StonedEdge/Retro-Lite-CM4-Dock/consolevectors/gb/DMG -High Tech Transparent (1995) (US).png

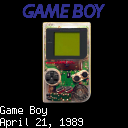
consolevectors/gb/DMG -High Tech Transparent (1995) (US).png
