StonedEdge/Retro-Lite-CM4-Dock/consolevectors/dreamcast/Dreamcast - Black.png

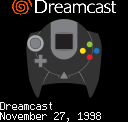
consolevectors/dreamcast/Dreamcast - Black.png
