StonedEdge/Retro-Lite-CM4-Dock/consolevectors/dreamcast/Dreamcast - Grey.png

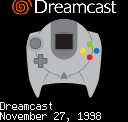
consolevectors/dreamcast/Dreamcast - Grey.png
