StonedEdge/Retro-Lite-CM4-Dock/consolevectors/dreamcast/Dreamcast - Red.png

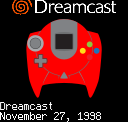
consolevectors/dreamcast/Dreamcast - Red.png
