StonedEdge/Retro-Lite-CM4-Dock/consolevectors/famicom/Famicom.png

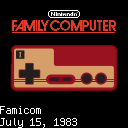
consolevectors/famicom/Famicom.png
