StonedEdge/Retro-Lite-CM4-Dock/consolevectors/gamegear/Game Gear.png

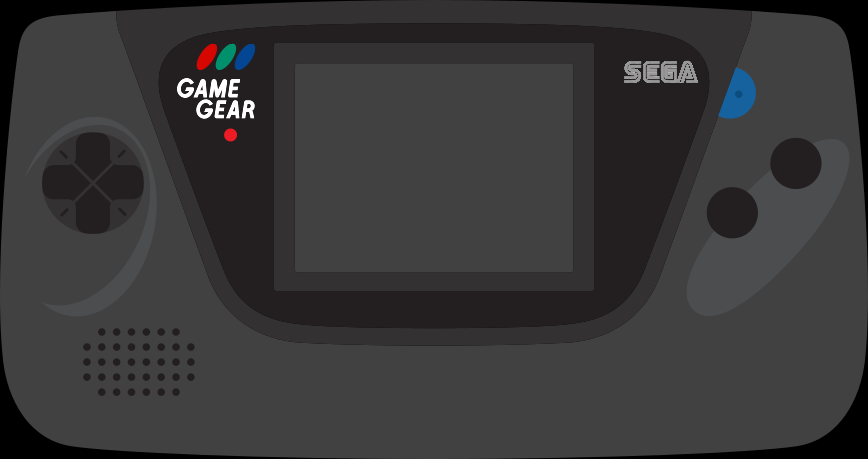
consolevectors/gamegear/Game Gear.png
