StonedEdge/Retro-Lite-CM4-Dock/consolevectors/gb/DMG - Cool Blue (1995) (EU).png

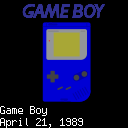
consolevectors/gb/DMG - Cool Blue (1995) (EU).png
