StonedEdge/Retro-Lite-CM4-Dock/consolevectors/gb/DMG - Deep Black (1995).png

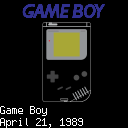
consolevectors/gb/DMG - Deep Black (1995).png
