StonedEdge/Retro-Lite-CM4-Dock/consolevectors/gb/DMG - Off White.png

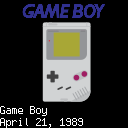
consolevectors/gb/DMG - Off White.png
