StonedEdge/Retro-Lite-CM4-Dock/consolevectors/gb/DMG - Radiant Red (1995).png

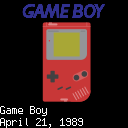
consolevectors/gb/DMG - Radiant Red (1995).png
