StonedEdge/Retro-Lite-CM4-Dock/consolevectors/gba/Gameboy Micro - Black.png

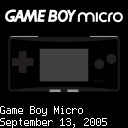
consolevectors/gba/Gameboy Micro - Black.png
