StonedEdge/Retro-Lite-CM4-Dock/consolevectors/gba/Gameboy Micro - Blue.png

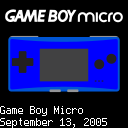
consolevectors/gba/Gameboy Micro - Blue.png
