StonedEdge/Retro-Lite-CM4-Dock/consolevectors/gba/Gameboy Micro - Famicom - red w gold faceplate (Japan, 2005).png

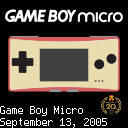
consolevectors/gba/Gameboy Micro - Famicom - red w gold faceplate (Japan, 2005).png
