StonedEdge/Retro-Lite-CM4-Dock/consolevectors/gba/Gameboy Micro - Mother 3 - red w red, worn faceplate (Japan, 2006).png

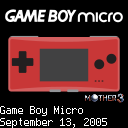
consolevectors/gba/Gameboy Micro - Mother 3 - red w red, worn faceplate (Japan, 2006).png
