StonedEdge/Retro-Lite-CM4-Dock/consolevectors/gba/Gameboy Micro - Pink (Europe, 2005).png

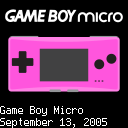
consolevectors/gba/Gameboy Micro - Pink (Europe, 2005).png
