StonedEdge/Retro-Lite-CM4-Dock/consolevectors/gba/Gameboy Micro - Pokémon - red w black faceplate & Pikachu silhouette (Japan, 2005).png

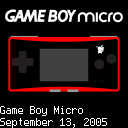
consolevectors/gba/Gameboy Micro - Pokémon - red w black faceplate & Pikachu silhouette (Japan, 2005).png
