StonedEdge/Retro-Lite-CM4-Dock/consolevectors/gba/Gameboy Micro - Red.png

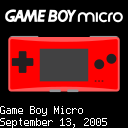
consolevectors/gba/Gameboy Micro - Red.png
