StonedEdge/Retro-Lite-CM4-Dock/consolevectors/gba/GBA - Fuchsia (2001) gba.png

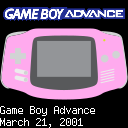
consolevectors/gba/GBA - Fuchsia (2001) gba.png
