StonedEdge/Retro-Lite-CM4-Dock/consolevectors/gba/GBA - Indigo - purple (2001).png

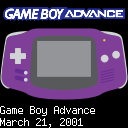
consolevectors/gba/GBA - Indigo - purple (2001).png
