StonedEdge/Retro-Lite-CM4-Dock/consolevectors/gba/GBA -Black (2001).png

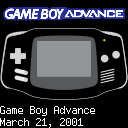
consolevectors/gba/GBA -Black (2001).png
