StonedEdge/Retro-Lite-CM4-Dock/consolevectors/gba/GBA -Pokémon Center (Latios & Latias) - blue w red buttons (2002).png

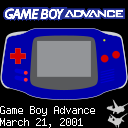
consolevectors/gba/GBA -Pokémon Center (Latios & Latias) - blue w red buttons (2002).png
