StonedEdge/Retro-Lite-CM4-Dock/consolevectors/gba/GBA SP - All Blacks (NZ).png

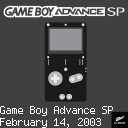
consolevectors/gba/GBA SP - All Blacks (NZ).png
