StonedEdge/Retro-Lite-CM4-Dock/consolevectors/gba/GBA SP - Cobalt Blue - frontlit (2003).png

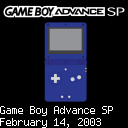
consolevectors/gba/GBA SP - Cobalt Blue - frontlit (2003).png
