StonedEdge/Retro-Lite-CM4-Dock/consolevectors/gba/GBA SP - Pearl Blue - backlit (2005) this was frontlit in Europe.png

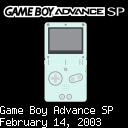
consolevectors/gba/GBA SP - Pearl Blue - backlit (2005) this was frontlit in Europe.png
