StonedEdge/Retro-Lite-CM4-Dock/consolevectors/gba/GBA SP - Pikachu - Yellow (Toys R Us 2005, Pokémon Center Japan).png

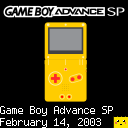
consolevectors/gba/GBA SP - Pikachu - Yellow (Toys R Us 2005, Pokémon Center Japan).png
