StonedEdge/Retro-Lite-CM4-Dock/consolevectors/gbc/Game Boy Color - Atomic Purple.png

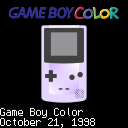
consolevectors/gbc/Game Boy Color - Atomic Purple.png
