StonedEdge/Retro-Lite-CM4-Dock/consolevectors/gbc/Game Boy Color - Midnight Blue (Toys 'R' Us, Japan, 1999).png

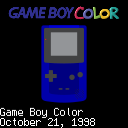
consolevectors/gbc/Game Boy Color - Midnight Blue (Toys 'R' Us, Japan, 1999).png
