StonedEdge/Retro-Lite-CM4-Dock/consolevectors/gbc/Game Boy Color - Pokemon Center GSC.png

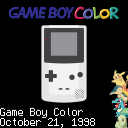
consolevectors/gbc/Game Boy Color - Pokemon Center GSC.png
