StonedEdge/Retro-Lite-CM4-Dock/consolevectors/gc/GameCube.png

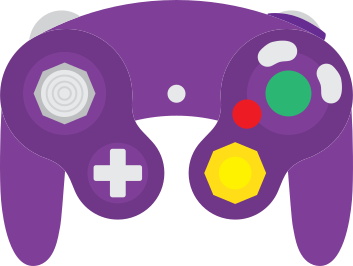
consolevectors/gc/GameCube.png
