StonedEdge/Retro-Lite-CM4-Dock/consolevectors/n64/N64 - Daiei Hawks.png

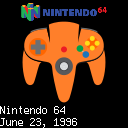
consolevectors/n64/N64 - Daiei Hawks.png
