StonedEdge/Retro-Lite-CM4-Dock/consolevectors/n64/N64 - Pokemon Stadium.png

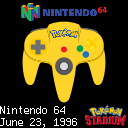
consolevectors/n64/N64 - Pokemon Stadium.png
