StonedEdge/Retro-Lite-CM4-Dock/consolevectors/n64/N64 -Smoke Black.png

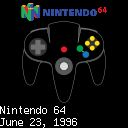
consolevectors/n64/N64 -Smoke Black.png
