StonedEdge/Retro-Lite-CM4-Dock/consolevectors/nds/Nintendo DS Lite - Black.png

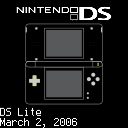
consolevectors/nds/Nintendo DS Lite - Black.png
