StonedEdge/Retro-Lite-CM4-Dock/consolevectors/nds/Nintendo DS Lite - Coral Pink.png

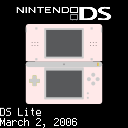
consolevectors/nds/Nintendo DS Lite - Coral Pink.png
