StonedEdge/Retro-Lite-CM4-Dock/consolevectors/nds/Nintendo DS Lite - Crimson.png

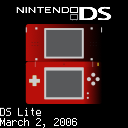
consolevectors/nds/Nintendo DS Lite - Crimson.png
