StonedEdge/Retro-Lite-CM4-Dock/consolevectors/nds/Nintendo DS Lite - Dialgia & Palkia.png

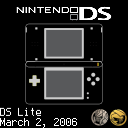
consolevectors/nds/Nintendo DS Lite - Dialgia & Palkia.png
