StonedEdge/Retro-Lite-CM4-Dock/consolevectors/nds/Nintendo DS Lite - Mario Edition.png

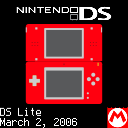
consolevectors/nds/Nintendo DS Lite - Mario Edition.png
