StonedEdge/Retro-Lite-CM4-Dock/consolevectors/nds/Nintendo DS Lite - Zelda Edition.png

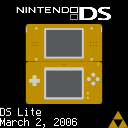
consolevectors/nds/Nintendo DS Lite - Zelda Edition.png
