StonedEdge/Retro-Lite-CM4-Dock/consolevectors/nds/Nintendo DSi - Dark Blue.png

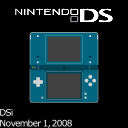
consolevectors/nds/Nintendo DSi - Dark Blue.png
