StonedEdge/Retro-Lite-CM4-Dock/consolevectors/nds/Nintendo DSi - Green.png

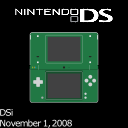
consolevectors/nds/Nintendo DSi - Green.png
