StonedEdge/Retro-Lite-CM4-Dock/consolevectors/nds/Nintendo DSi - Red.png

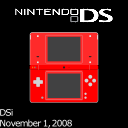
consolevectors/nds/Nintendo DSi - Red.png
