StonedEdge/Retro-Lite-CM4-Dock/consolevectors/neogeo/NeoGeo.png

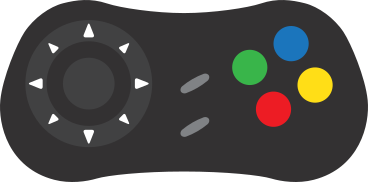
consolevectors/neogeo/NeoGeo.png
