StonedEdge/Retro-Lite-CM4-Dock/consolevectors/nes/NES.png

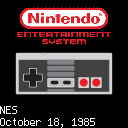
consolevectors/nes/NES.png
