StonedEdge/Retro-Lite-CM4-Dock/consolevectors/psp/PlayStation Portable - Black.png

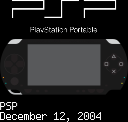
consolevectors/psp/PlayStation Portable - Black.png
