StonedEdge/Retro-Lite-CM4-Dock/consolevectors/psp/PlayStation Portable - Felicia Blue.png

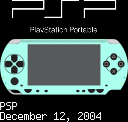
consolevectors/psp/PlayStation Portable - Felicia Blue.png
