StonedEdge/Retro-Lite-CM4-Dock/consolevectors/psp/PlayStation Portable - God of War.png

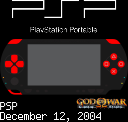
consolevectors/psp/PlayStation Portable - God of War.png
