StonedEdge/Retro-Lite-CM4-Dock/consolevectors/psp/PlayStation Portable - Red.png

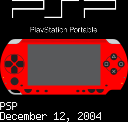
consolevectors/psp/PlayStation Portable - Red.png
