StonedEdge/Retro-Lite-CM4-Dock/consolevectors/sega32x/Sega32X.png

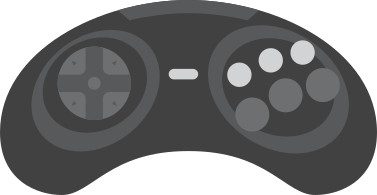
consolevectors/sega32x/Sega32X.png
