StonedEdge/Retro-Lite-CM4-Dock/consolevectors/snes/SNES - Light Purple.png

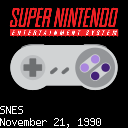
consolevectors/snes/SNES - Light Purple.png
