StonedEdge/Retro-Lite-CM4-Dock/consolevectors/switch/Nintendo Switch Lite - Coral.png

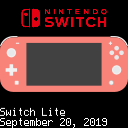
consolevectors/switch/Nintendo Switch Lite - Coral.png
