StonedEdge/Retro-Lite-CM4-Dock/consolevectors/switch/Nintendo Switch Lite - Dialga & Palkia Edition.png

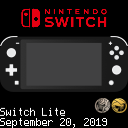
consolevectors/switch/Nintendo Switch Lite - Dialga & Palkia Edition.png
