StonedEdge/Retro-Lite-CM4-Dock/consolevectors/vb/Famicom.png

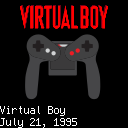
consolevectors/vb/Famicom.png
